anasarif23/Spectrum-Audio-Amp/PICS & PDFS/AGND.png

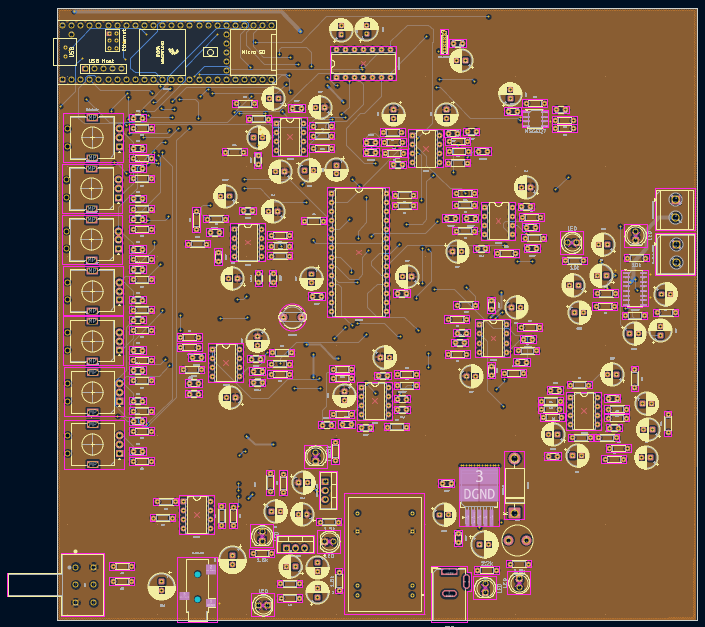
PICS & PDFS/AGND.png
